rumblesan/ouroboros/design-docs/subsection-analysis/logarithmic-resonance-control/logarithmic-resonance-control.kicad_pcb

## KiCad design 23cm-trx-kicad/23cm-trx-kicad.kicad_sch

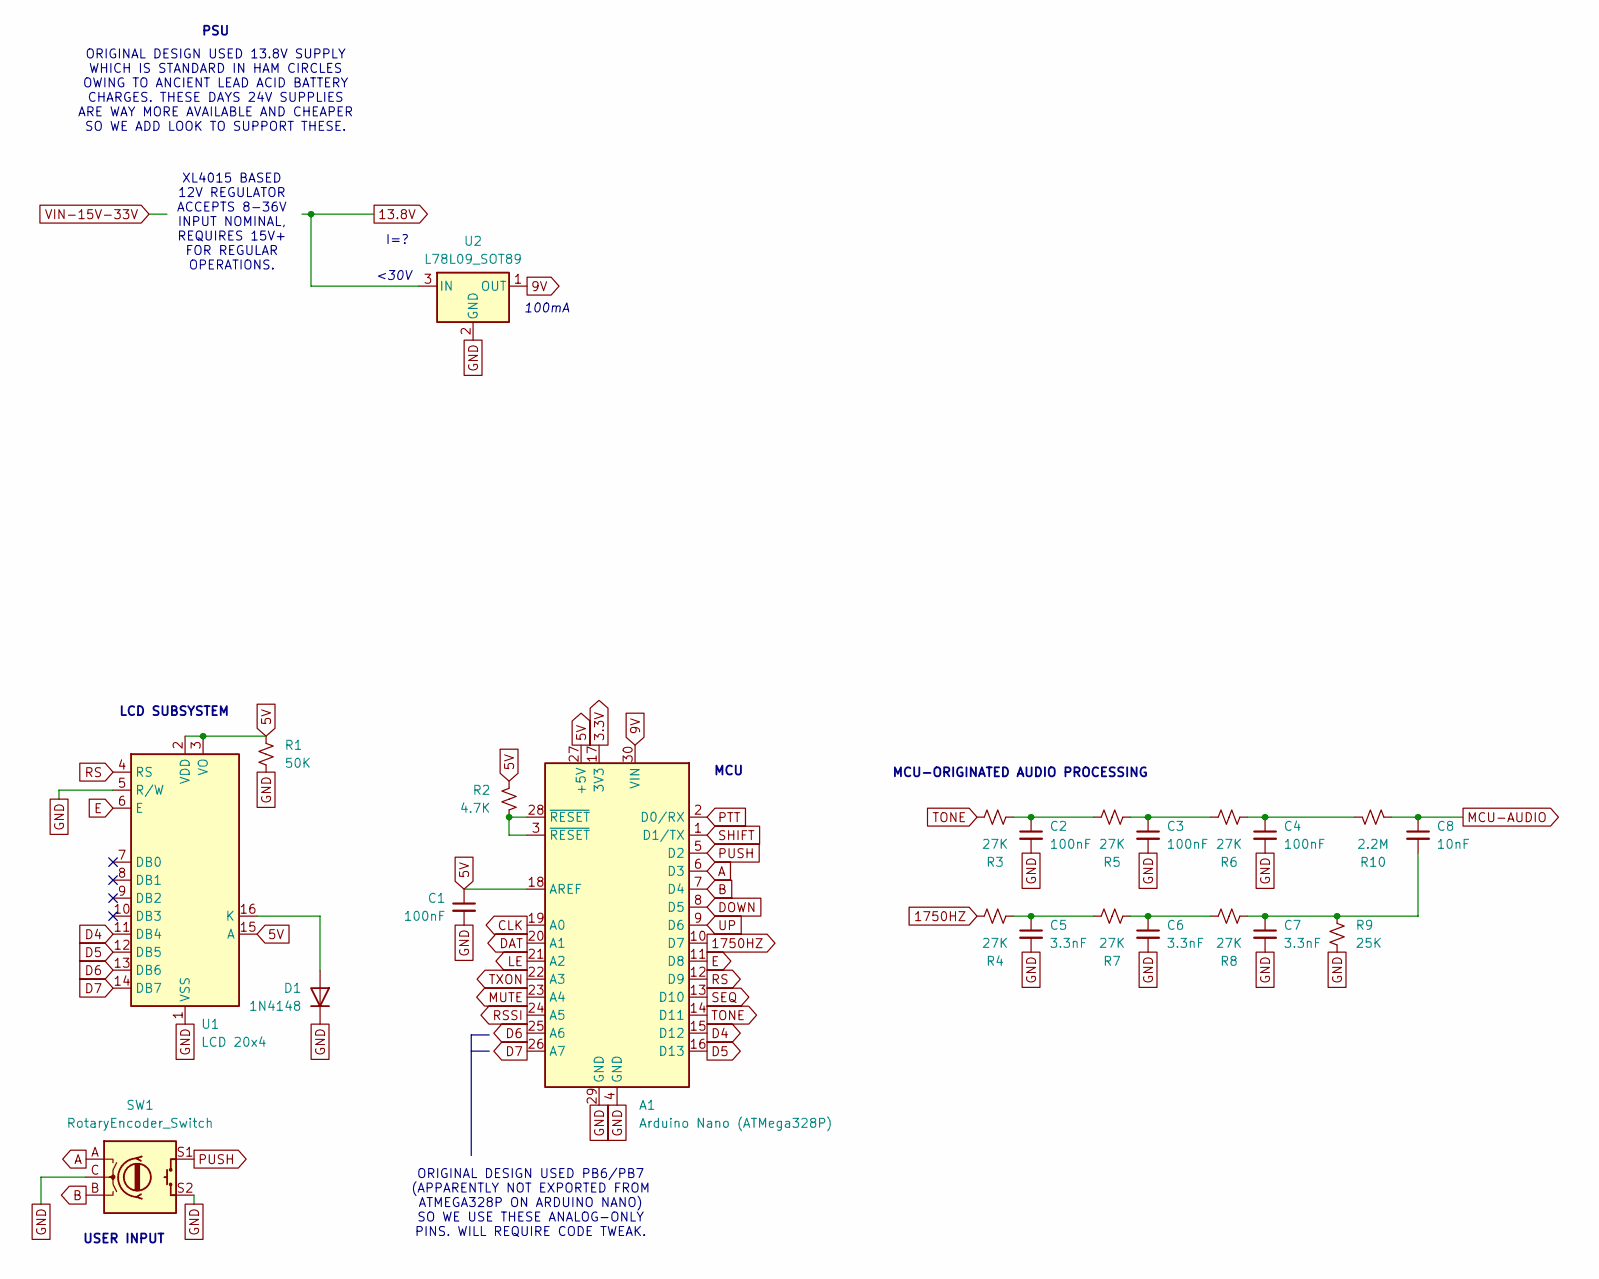
[picture p23: schematic 23cm-trx-kicad.kicad_sch]

Parts:
A1: Arduino Nano (ATMega328P); Arduino_Nano
C1, C2, C3, C4: 100nF
C5, C6, C7: 3.3nF
C8: 10nF
D1: 1N4148; D_DO-35_SOD27_P7.62mm_Horizontal
R1: 50K
R2: 4.7K
R3, R4, R5, R6, R7, R8: 27K
R9: 25K
R10: 2.2M
SW1: RotaryEncoder_Switch
U1: LCD 20x4; NHD-0420H1Z
U2: L78L09_SOT89; SOT-89-3

Connections:
3.3V: A1.17 (3V3)
5V: A1.18 (AREF), A1.27 (+5V), C1.1, R1.1, R2.1, U1.2 (VDD), U1.3 (VO), U1.15 (A)
9V: A1.30 (VIN), U2.1 (OUT)
13.8V: U2.3 (IN)
1750HZ: A1.10 (D7), R4.1
A: A1.6 (D3), SW1.A
B: A1.7 (D4), SW1.B
CLK: A1.19 (A0)
D4: A1.15 (D12), U1.11 (DB4)
D5: A1.16 (D13), U1.12 (DB5)
D6: A1.25 (A6), U1.13 (DB6)
D7: A1.26 (A7), U1.14 (DB7)
DAT: A1.20 (A1)
DOWN: A1.8 (D5)
E: A1.11 (D8), U1.6 (E)
GND: A1.4 (GND), A1.29 (GND), C1.2, C2.2, C3.2, C4.2, C5.2, C6.2, C7.2, D1.1 (K), R1.2, R9.2, SW1.C, SW1.S2, U1.1 (VSS), U1.5 (R/W), U2.2 (GND)
LE: A1.21 (A2)
MCU-AUDIO: C8.1, R10.1
MUTE: A1.23 (A4)
unnamed: A1.3 (~RESET), A1.28 (~RESET), R2.2
unnamed: C2.1, R3.2, R5.1
unnamed: C3.1, R5.2, R6.1
unnamed: C4.1, R6.2, R10.2
unnamed: C5.1, R4.2, R7.1
unnamed: C6.1, R7.2, R8.1
unnamed: C7.1, C8.2, R8.2, R9.1
unnamed: D1.2 (A), U1.16 (K)
PTT: A1.2 (D0/RX)
PUSH: A1.5 (D2), SW1.S1
RS: A1.12 (D9), U1.4 (RS)
RSSI: A1.24 (A5)
SEQ: A1.13 (D10)
SHIFT: A1.1 (D1/TX)
TONE: A1.14 (D11), R3.1
TXON: A1.22 (A3)
UP: A1.9 (D6)

Notes on the sheet:
ORIGINAL DESIGN USED 13.8V SUPPLY WHICH IS STANDARD IN HAM CIRCLES OWING TO ANCIENT LEAD ACID BATTERY CHARGES. THESE DAYS 24V SUPPLIES ARE WAY MORE AVAILABLE AND CHEAPER SO WE ADD LOOK TO SUPPORT THESE.
MCU
LCD SUBSYSTEM
XL4015 BASED 12V REGULATOR ACCEPTS 8-36V INPUT NOMINAL, REQUIRES 15V+ FOR REGULAR OPERATIONS.
<30V
PSU
100mA
I=?
USER INPUT
MCU-ORIGINATED AUDIO PROCESSING
ORIGINAL DESIGN USED PB6/PB7 (APPARENTLY NOT EXPORTED FROM ATMEGA328P ON ARDUINO NANO) SO WE USE THESE ANALOG-ONLY PINS. WILL REQUIRE CODE TWEAK.
